sidharthmrao/LINUS/input/bruce.png

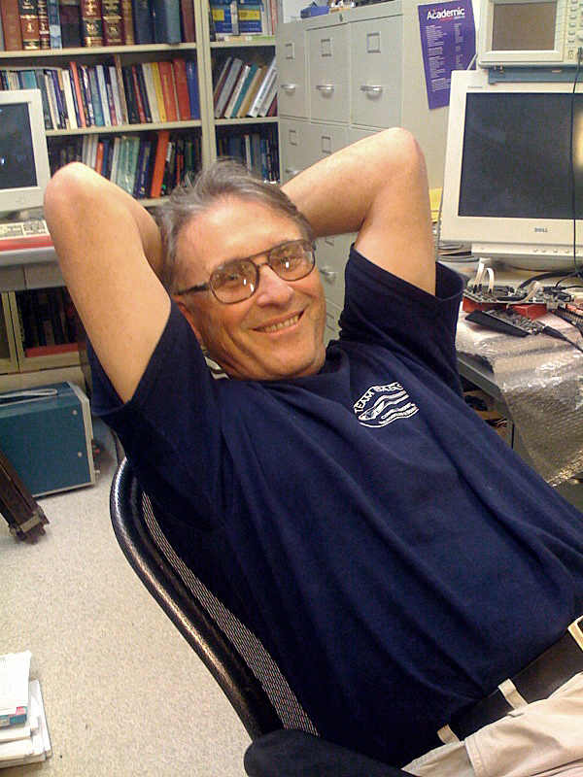
input/bruce.png
