sidharthmrao/LINUS/input/cat.jpg

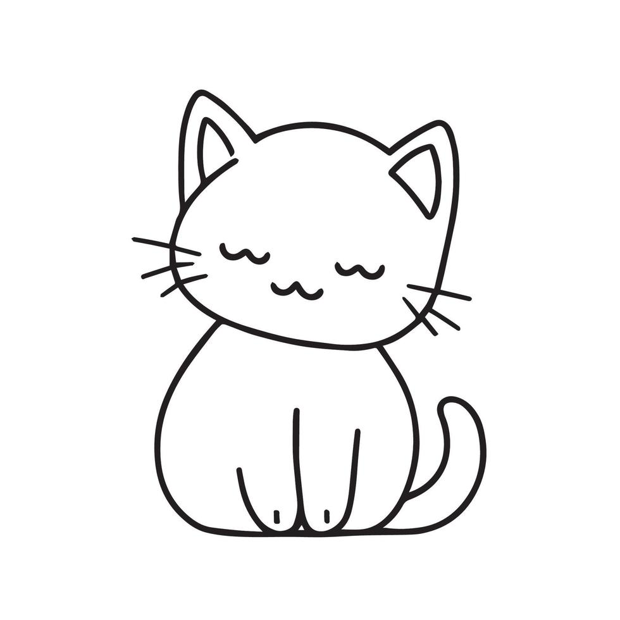
input/cat.jpg
