sidharthmrao/LINUS/input/handsome_squidward.png

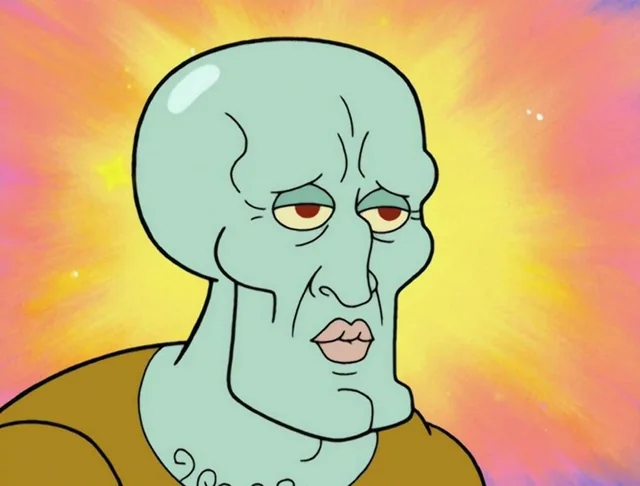
input/handsome_squidward.png
