sidharthmrao/LINUS/input/homer.jpg

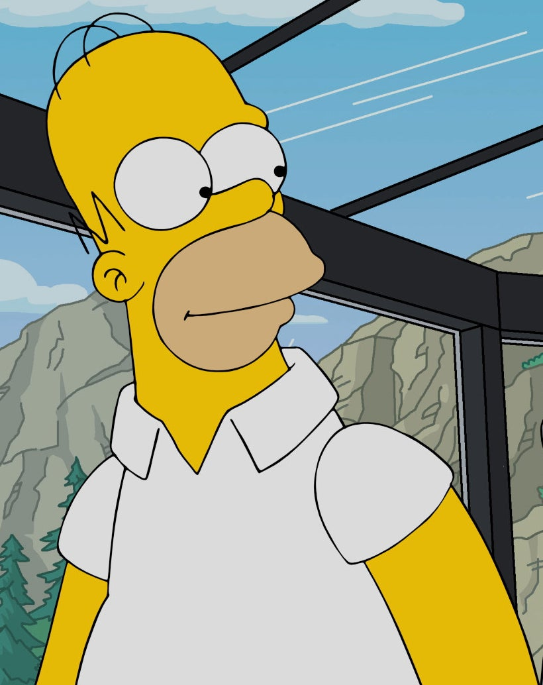
input/homer.jpg
