sidharthmrao/LINUS/input/hunter.png

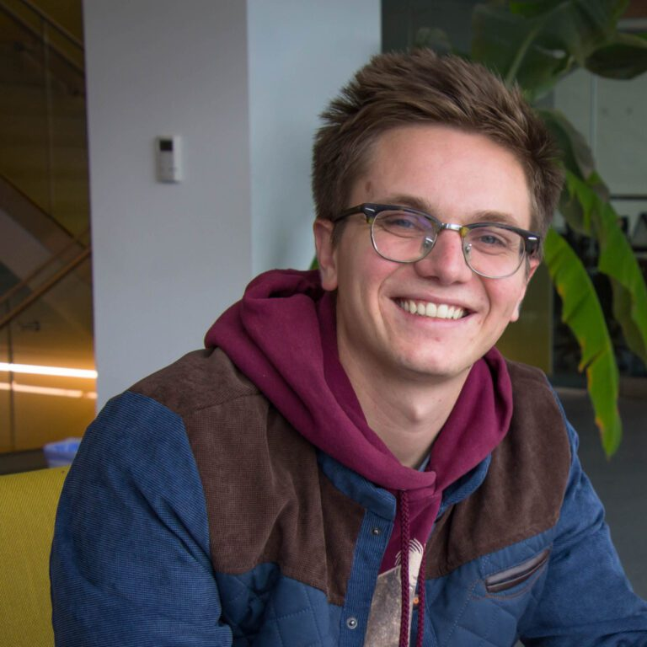
input/hunter.png
