sidharthmrao/LINUS/input/obama.png

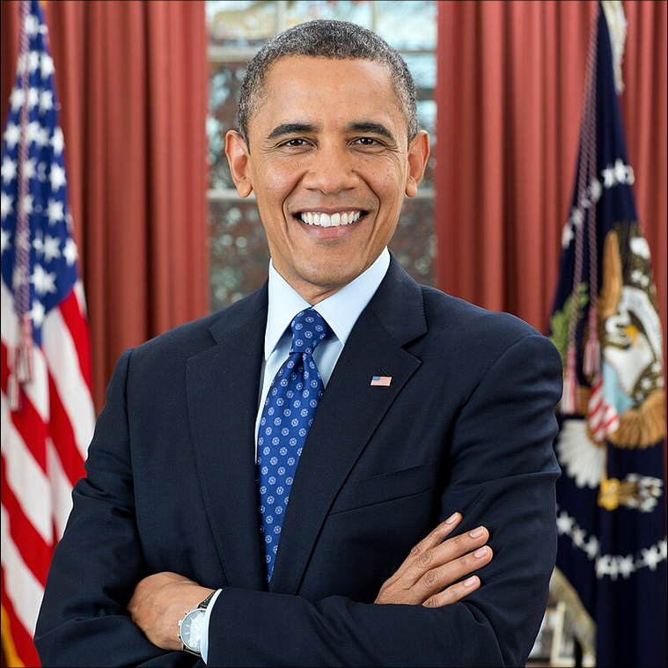
input/obama.png
