sidharthmrao/LINUS/input/pika.png

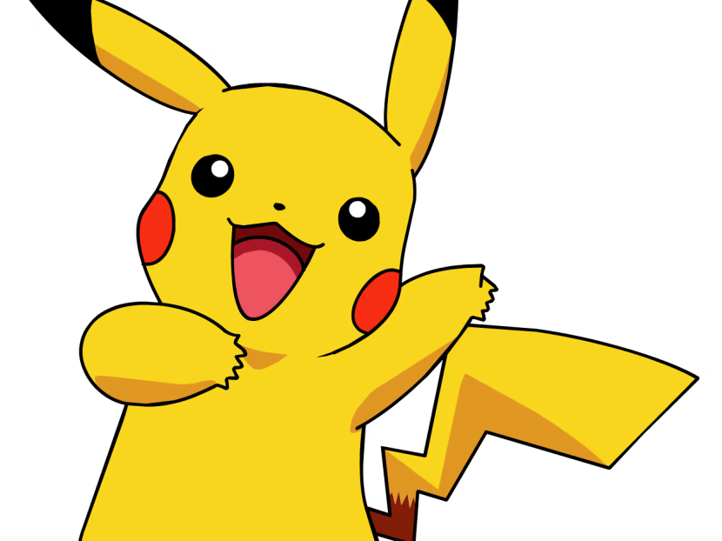
input/pika.png
