sidharthmrao/LINUS/input/shrek.png

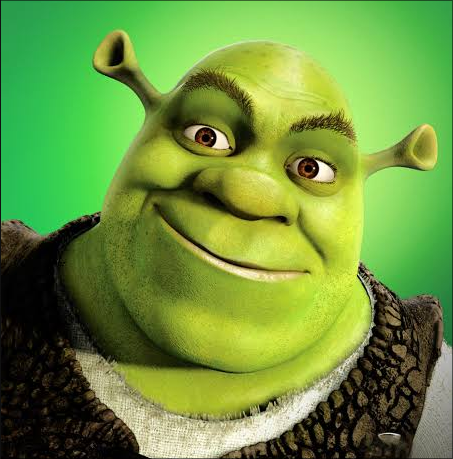
input/shrek.png
