sidharthmrao/LINUS/input/void.jpg

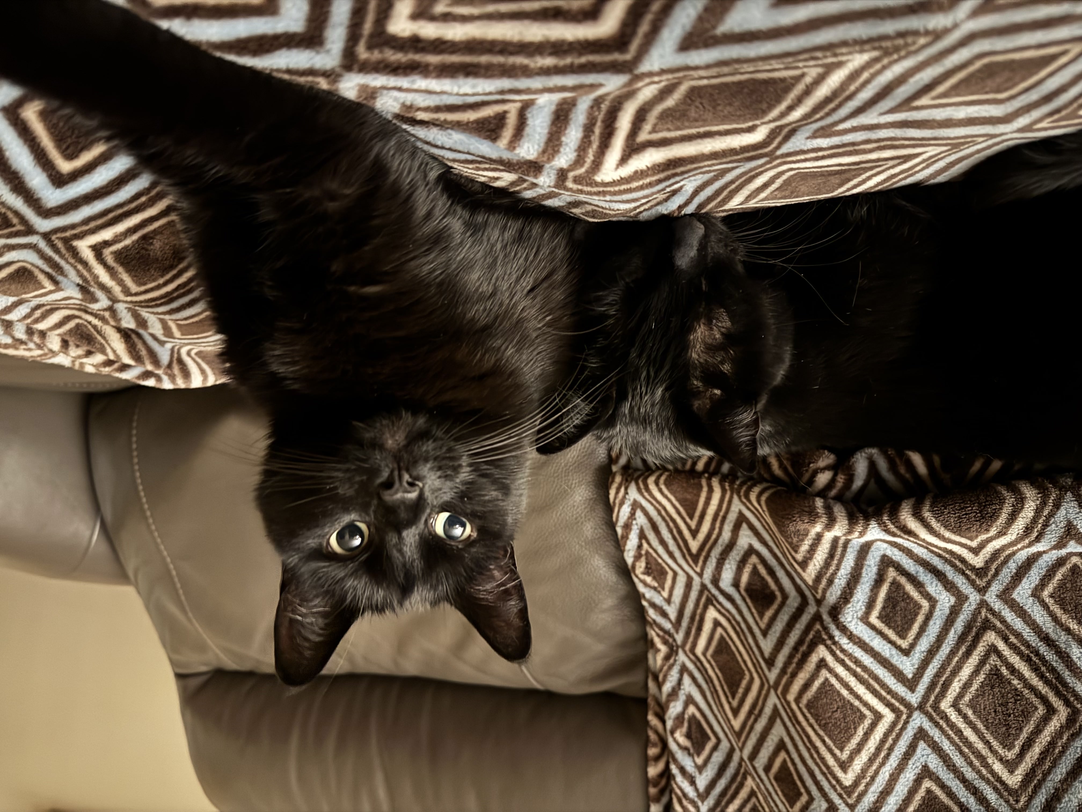
input/void.jpg
