sidharthmrao/LINUS/output/bruce_skel.png

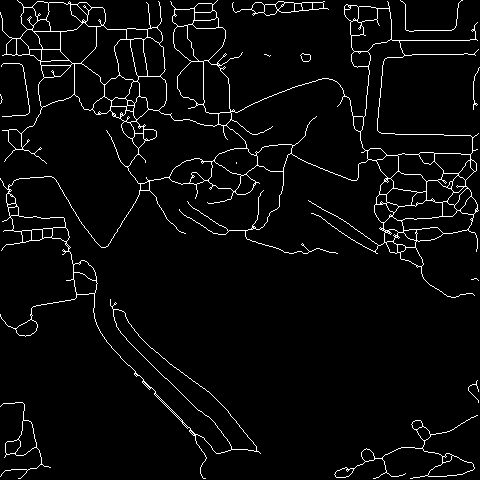
output/bruce_skel.png
