sidharthmrao/LINUS/output/cat_recording.gif

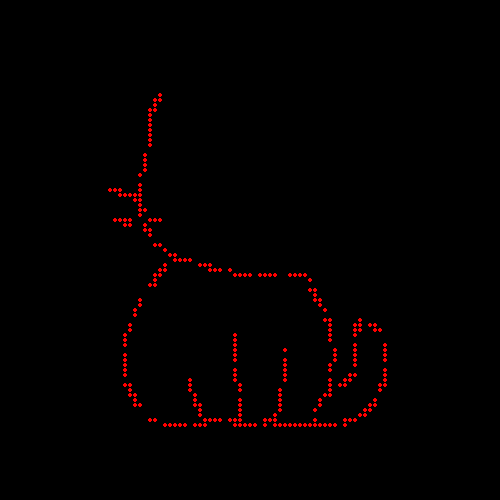
output/cat_recording.gif
