sidharthmrao/LINUS/output/cat_reduced.png

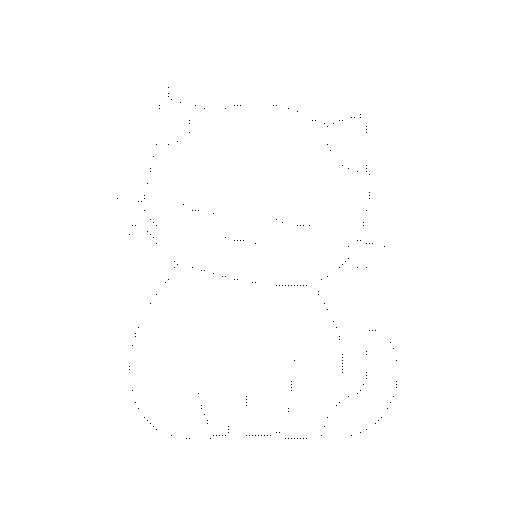
output/cat_reduced.png
