sidharthmrao/LINUS/output/cat_skel.png

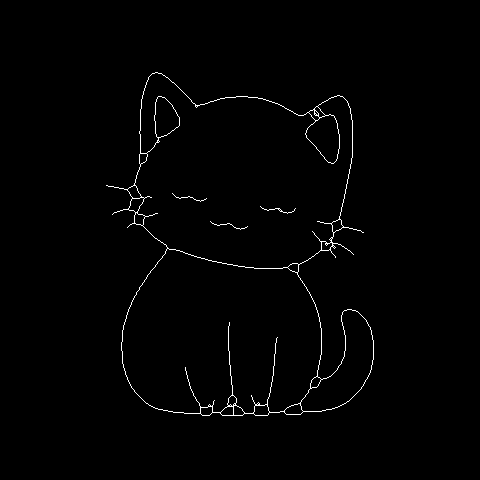
output/cat_skel.png
