sidharthmrao/LINUS/output/cat_skeletonized.jpg

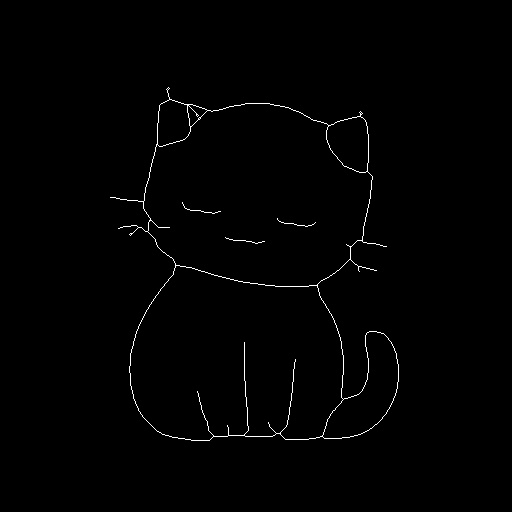
output/cat_skeletonized.jpg
