sidharthmrao/LINUS/output/handsome_squidward_recording.gif

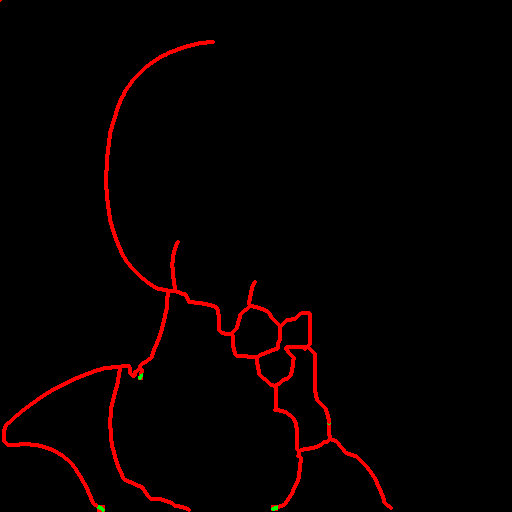
output/handsome_squidward_recording.gif
