sidharthmrao/LINUS/output/handsome_squidward_skel.png

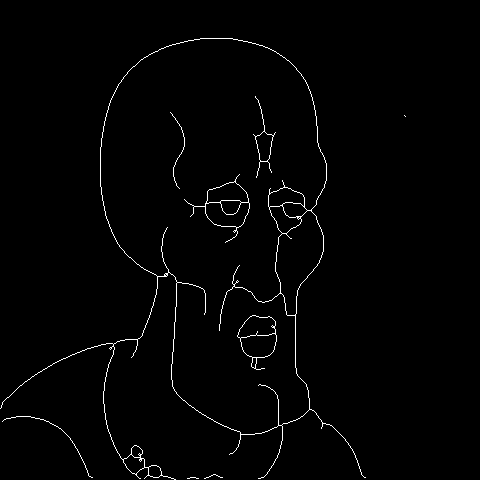
output/handsome_squidward_skel.png
