sidharthmrao/LINUS/output/homer_skel.png

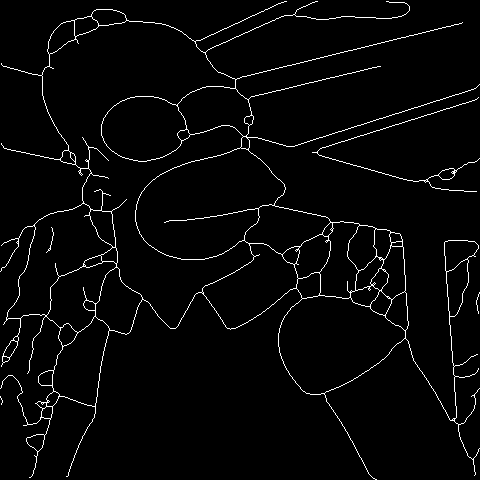
output/homer_skel.png
