sidharthmrao/LINUS/output/hunter_skel.png

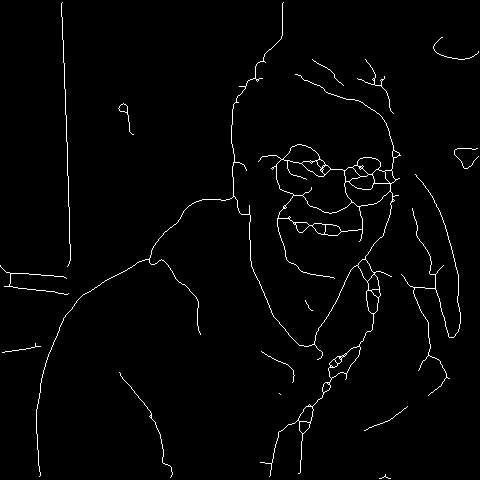
output/hunter_skel.png
