sidharthmrao/LINUS/output/obama_skel.png

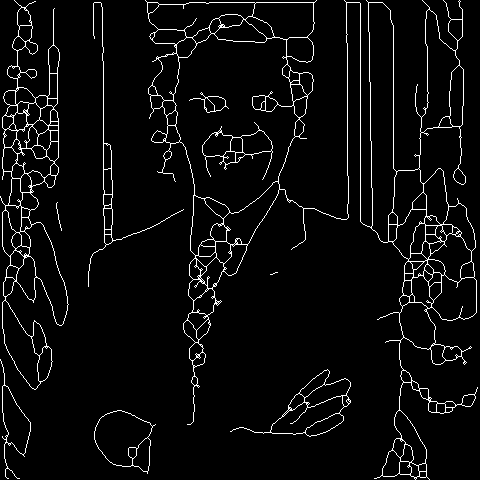
output/obama_skel.png
