sidharthmrao/LINUS/output/pika_skel.png

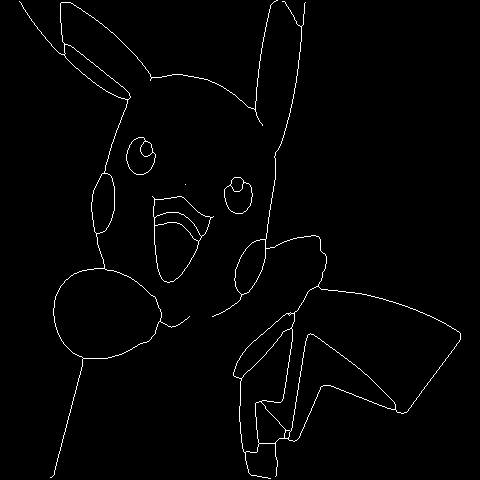
output/pika_skel.png
