sidharthmrao/LINUS/output/recording.gif

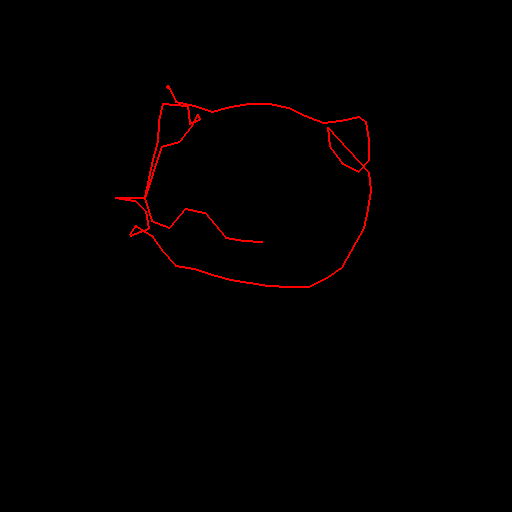
output/recording.gif
