sidharthmrao/LINUS/output/shrek_clustered.jpg

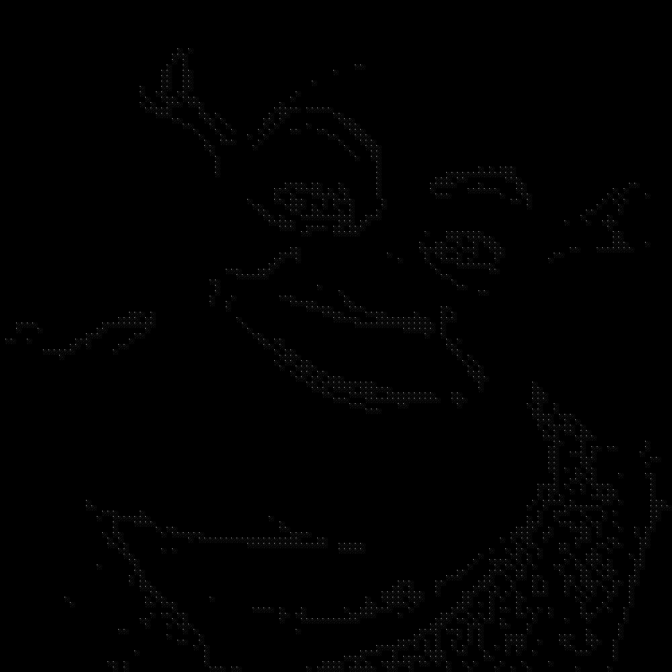
output/shrek_clustered.jpg
