sidharthmrao/LINUS/output/shrek_downsampled.jpg

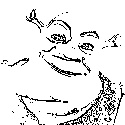
output/shrek_downsampled.jpg
