sidharthmrao/LINUS/output/shrek_filtered.jpg

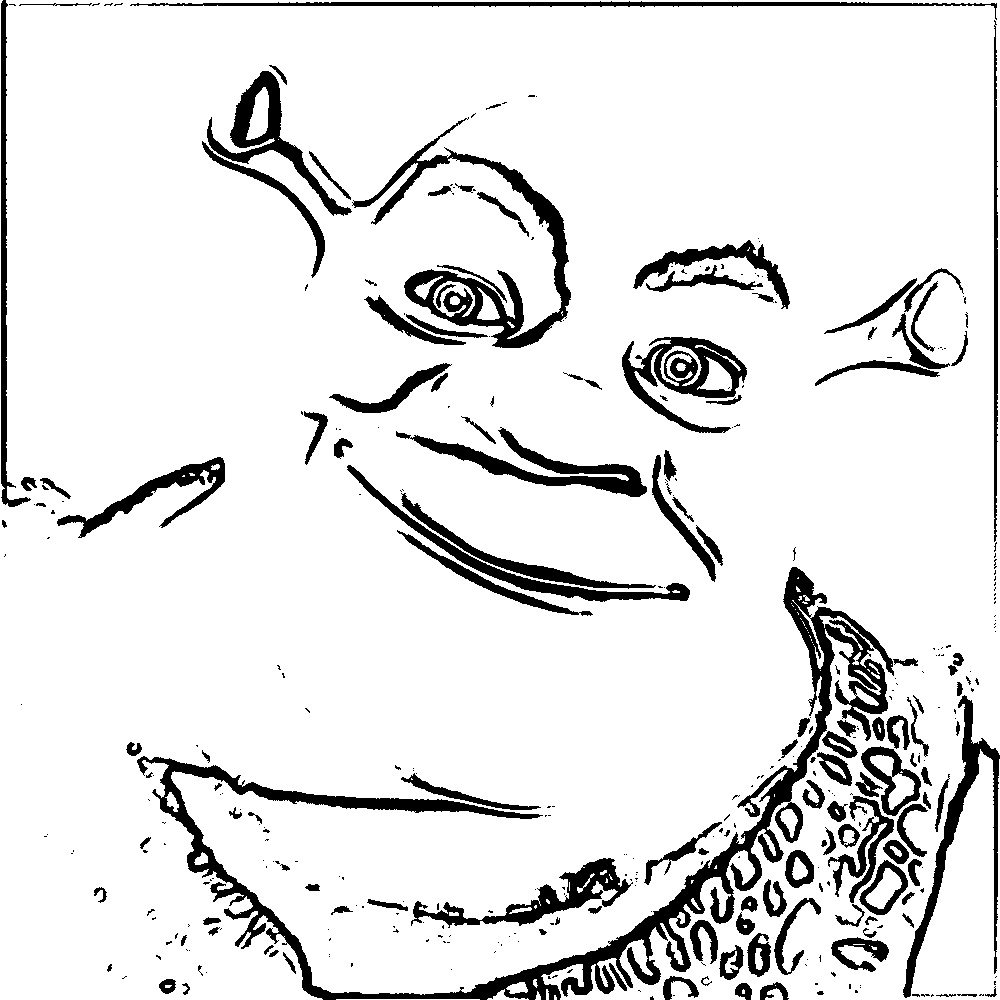
output/shrek_filtered.jpg
