sidharthmrao/LINUS/output/shrek_recording.gif

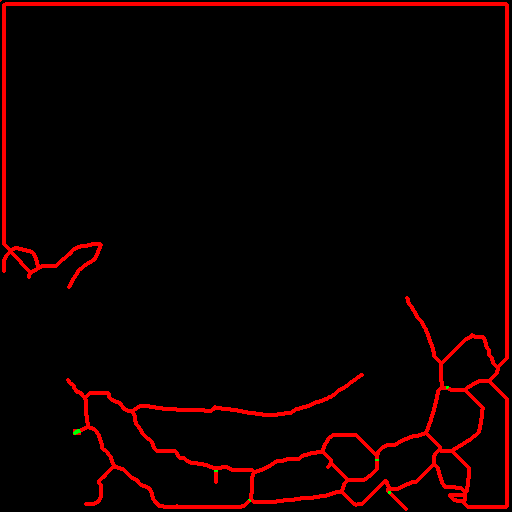
output/shrek_recording.gif
