sidharthmrao/LINUS/output/shrek_reduced.png

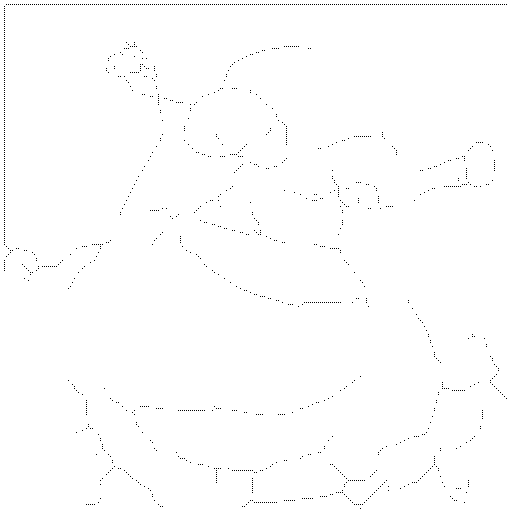
output/shrek_reduced.png
