sidharthmrao/LINUS/output/shrek_skel.png

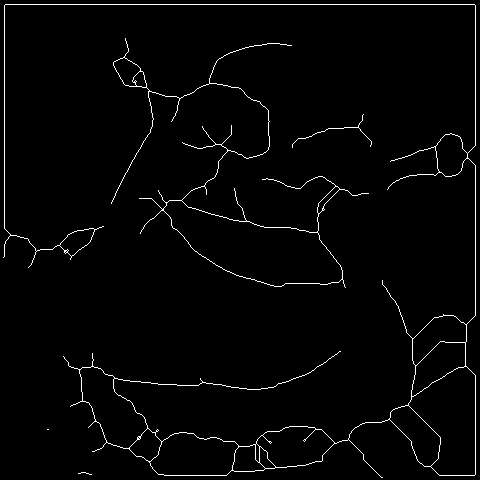
output/shrek_skel.png
