sidharthmrao/LINUS/output/skel.gif

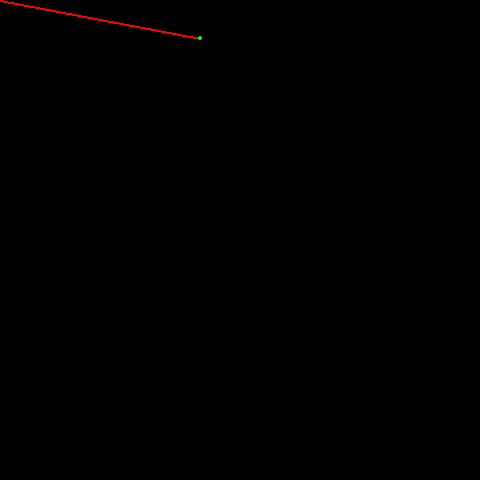
output/skel.gif
